dorukkumkumoglu/optocamzero/assets/exploded-1.jpg

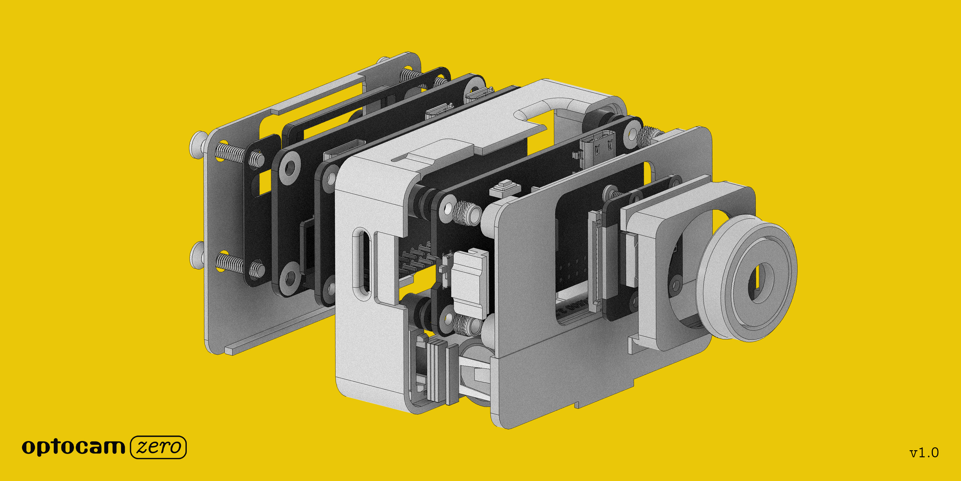
assets/exploded-1.jpg
