dorukkumkumoglu/optocamzero/hardware/stls/joystick-button_v1.0.stl

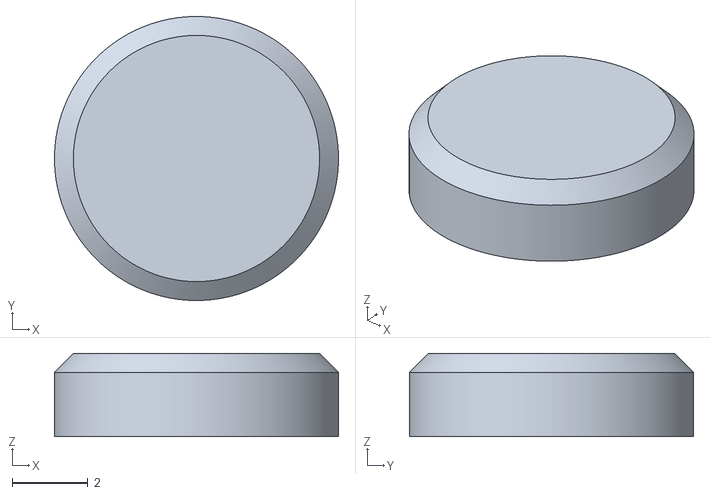
[picture p30: CAD file, 2026-03-29]
hardware/stls/joystick-button_v1.0.stl
7.50 x 7.50 x 2.20
