dorukkumkumoglu/optocamzero/hardware/stls/battery-level-visor_v1.0.stl

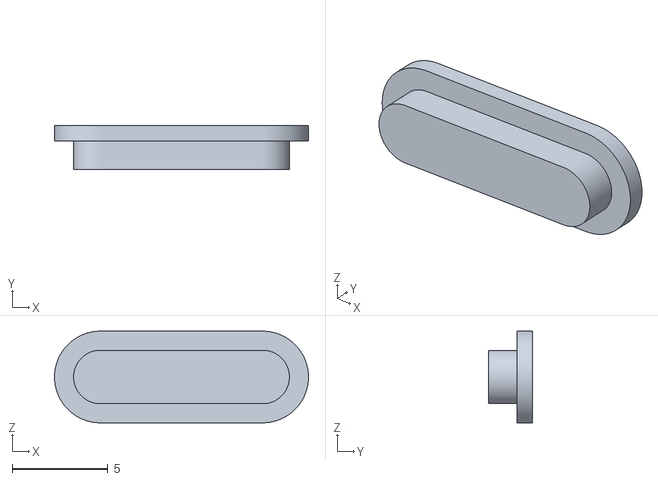
[picture p31: CAD file, 2026-03-29]
hardware/stls/battery-level-visor_v1.0.stl
13.3 x 2.30 x 4.80
