dorukkumkumoglu/optocamzero/software/firmware-buildroot/overlay/usr/share/optocam/calib_color.png

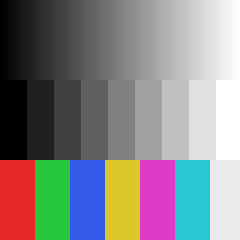
software/firmware-buildroot/overlay/usr/share/optocam/calib_color.png
